SushanThakur/armikochan/3_3D_model/main-assembly.SLDASM

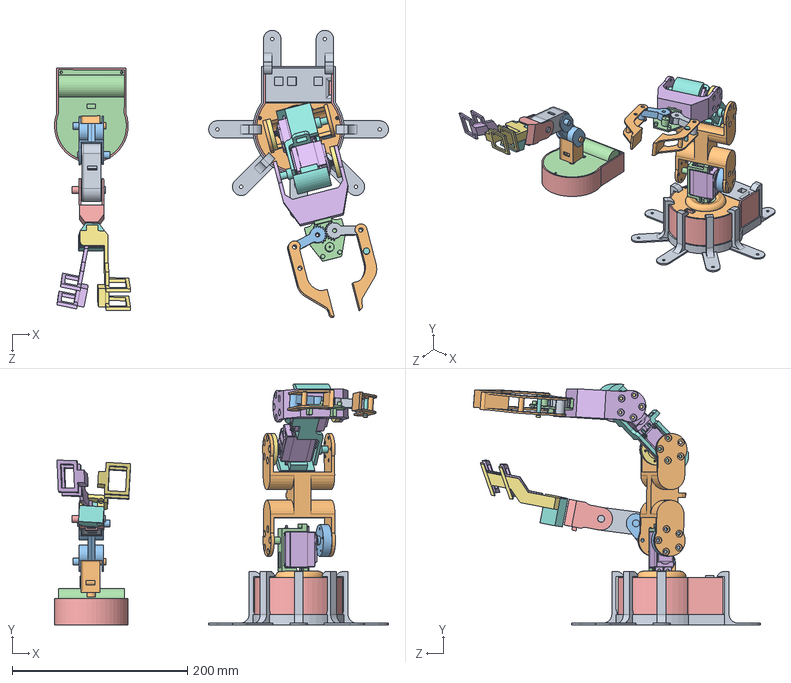
[picture p57: CAD file, 2025-09-16]
3_3D_model/main-assembly.SLDASM
380.7 x 274.4 x 327.6 mm
base
holder
left-gear-small
tip-v2 x 2
right-gear-small
holder-clip
holder-clip-holder
Servo MG996R x 4
Servo MG996R Shaft x 4
rotating_base
round-horn-extended
left-plate
base-cover
holder-arm
round-horn-self x 2
wrist-main-body
contorller-base
controller-base-cover
soldier
contorller-base-rotate
controller-arm
contorller-finger
controller-finger-tip-cover
controller-movable-finger
contorller wrist
breadboard
battery
base-cover-servo
base-supporter
