SushanThakur/armikochan/3_3D_model/controller/controller-wrist/contorller wrist.SLDPRT

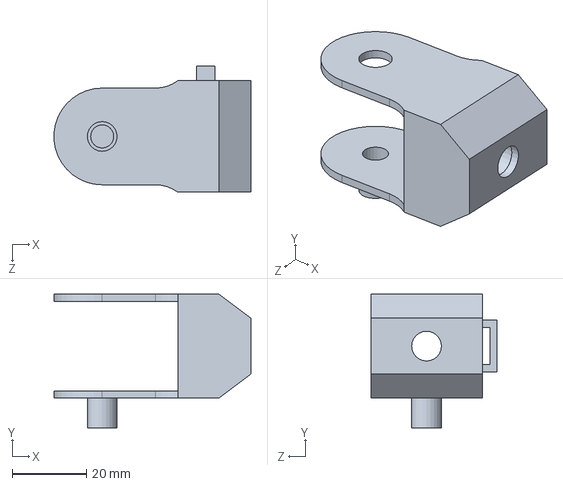
[picture p66: CAD file, 2025-09-16]
3_3D_model/controller/controller-wrist/contorller wrist.SLDPRT
53.0 x 36.0 x 34.0 mm
