SushanThakur/armikochan/3_3D_model/controller/stl/abs/controller-arm-1.STL

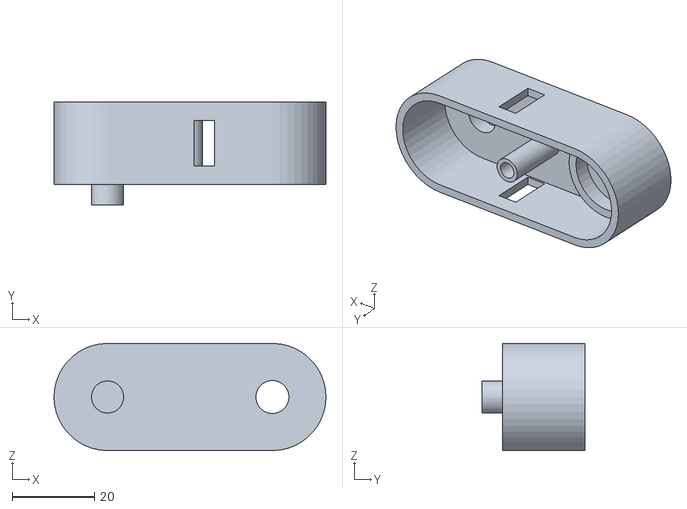
[picture p67: CAD file, 2024-01-20]
3_3D_model/controller/stl/abs/controller-arm-1.STL
66.0 x 25.0 x 26.0
