SushanThakur/armikochan/3_3D_model/shoulder/left-plate.SLDPRT

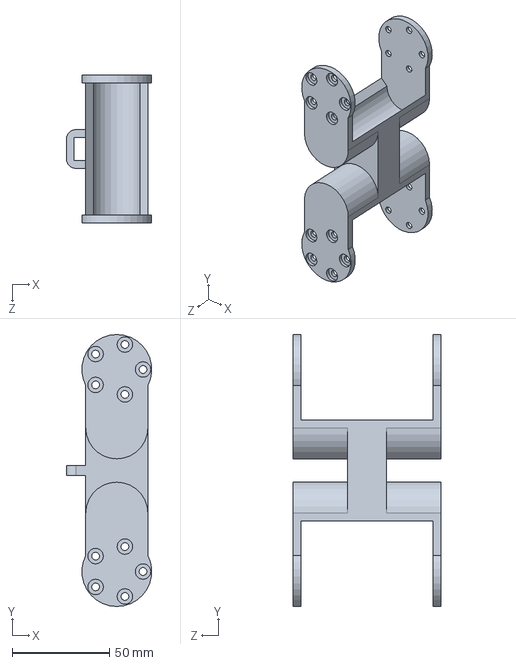
[picture p68: CAD file, 2025-09-16]
3_3D_model/shoulder/left-plate.SLDPRT
44.0 x 140.0 x 76.0 mm
