SushanThakur/armikochan/3_3D_model/test-prints/bearing-inner.SLDPRT

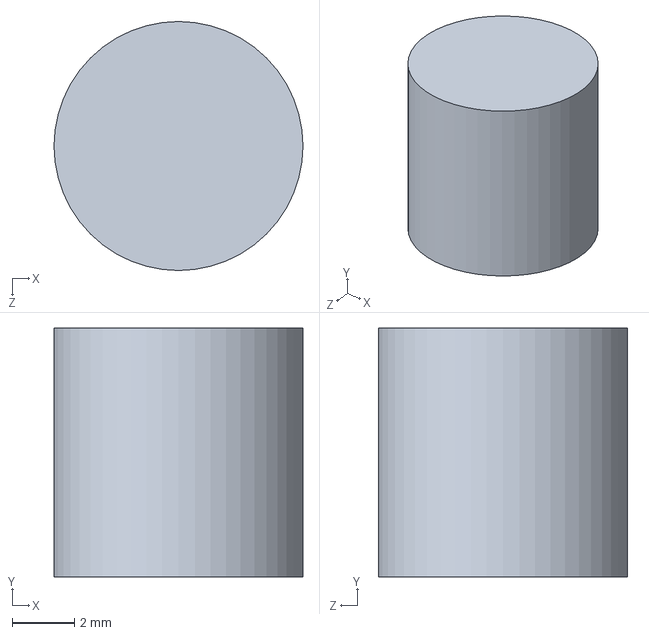
[picture p69: CAD file, 2024-01-20]
3_3D_model/test-prints/bearing-inner.SLDPRT
8.00 x 8.00 x 8.00 mm
