SushanThakur/armikochan/3_3D_model/arm/holder-arm.SLDPRT

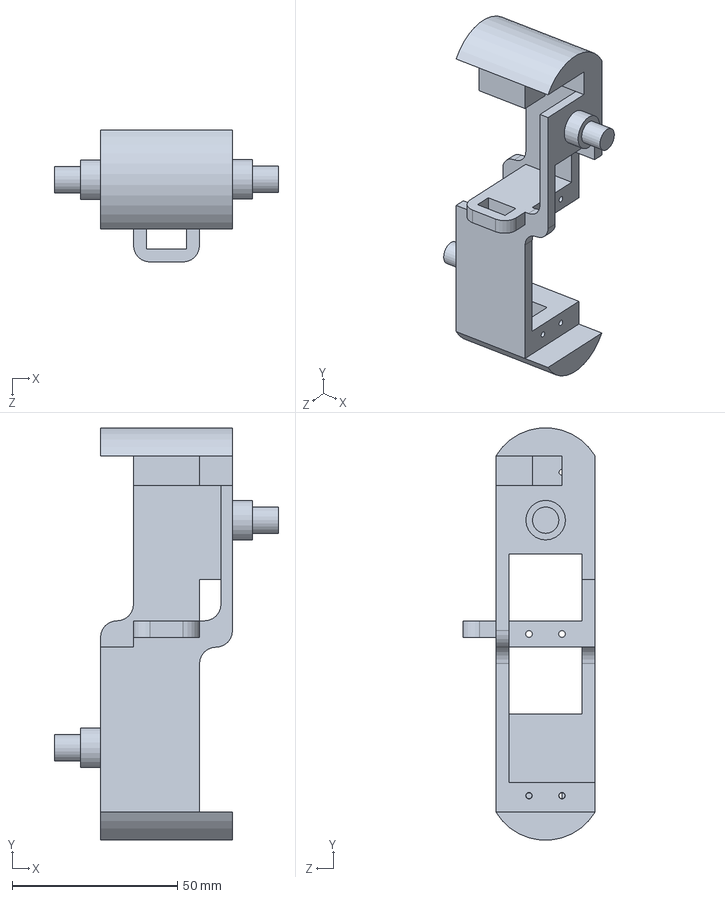
[picture p70: CAD file, 2025-09-16]
3_3D_model/arm/holder-arm.SLDPRT
68.0 x 124.8 x 40.0 mm
