SushanThakur/armikochan/3_3D_model/base-cover.SLDPRT

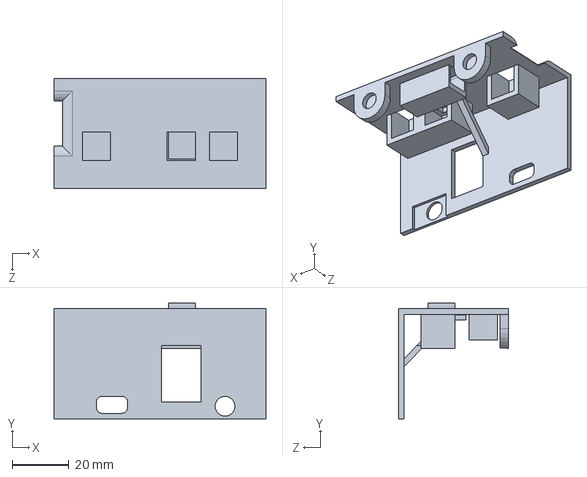
[picture p71: CAD file, 2025-09-16]
3_3D_model/base-cover.SLDPRT
75.0 x 41.0 x 39.0 mm
