SushanThakur/armikochan/3_3D_model/claw/holder-clip-holder.SLDPRT

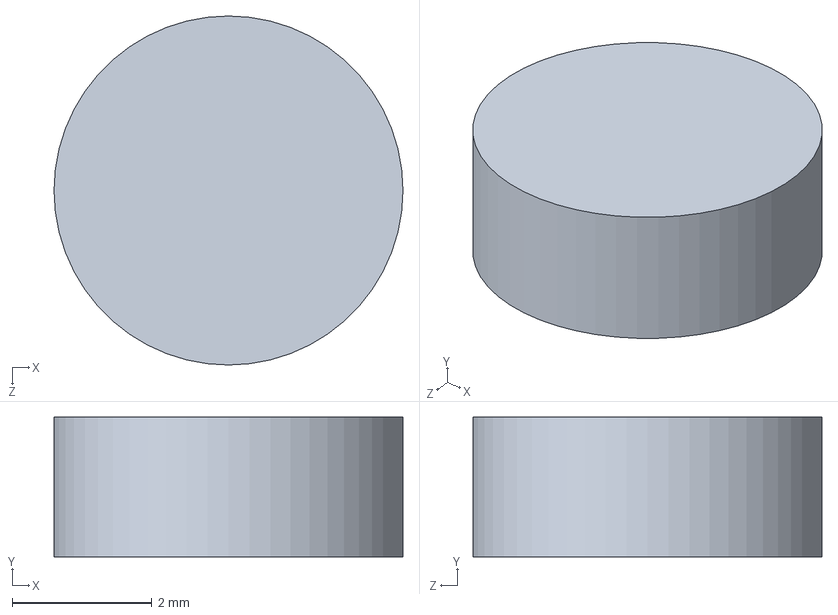
[picture p72: CAD file, 2025-09-16]
3_3D_model/claw/holder-clip-holder.SLDPRT
5.00 x 2.00 x 5.00 mm
