SushanThakur/armikochan/3_3D_model/controller/contorller-finger/controller-finger-tip-cover.SLDPRT

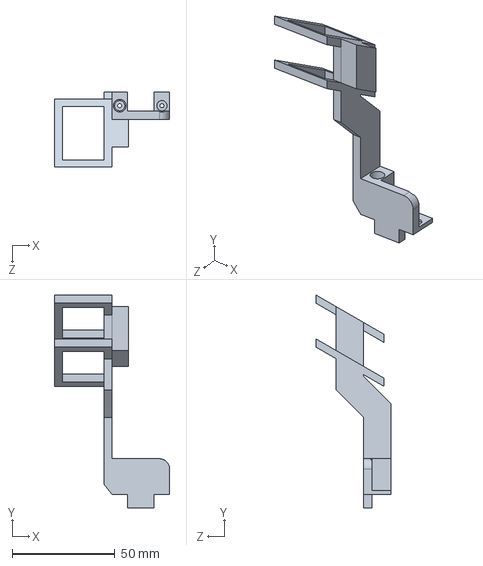
[picture p73: CAD file, 2025-09-16]
3_3D_model/controller/contorller-finger/controller-finger-tip-cover.SLDPRT
56.0 x 103.4 x 36.4 mm
