SushanThakur/armikochan/3_3D_model/controller/stl/abs/controller-arm.STL

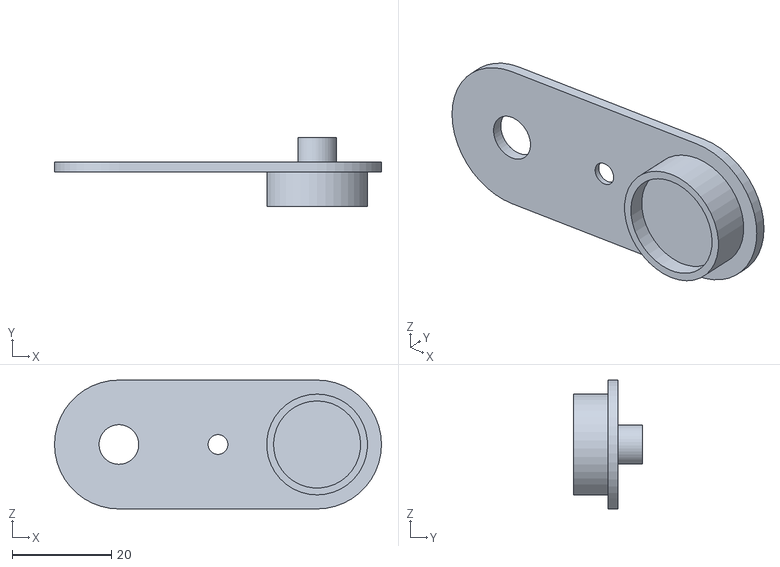
[picture p74: CAD file, 2024-01-20]
3_3D_model/controller/stl/abs/controller-arm.STL
66.0 x 14.0 x 26.0
