SushanThakur/armikochan/3_3D_model/controller/stl/second-concept-bot.STL

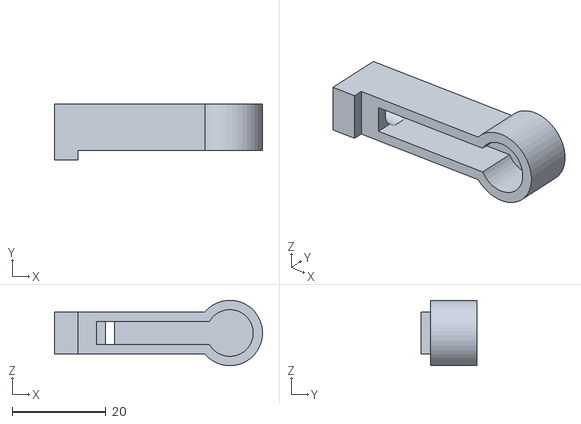
[picture p75: CAD file, 2024-02-05]
3_3D_model/controller/stl/second-concept-bot.STL
44.5 x 12.0 x 14.0
