SushanThakur/armikochan/3_3D_model/MG996R SERVO/Servo MG996R.SLDPRT

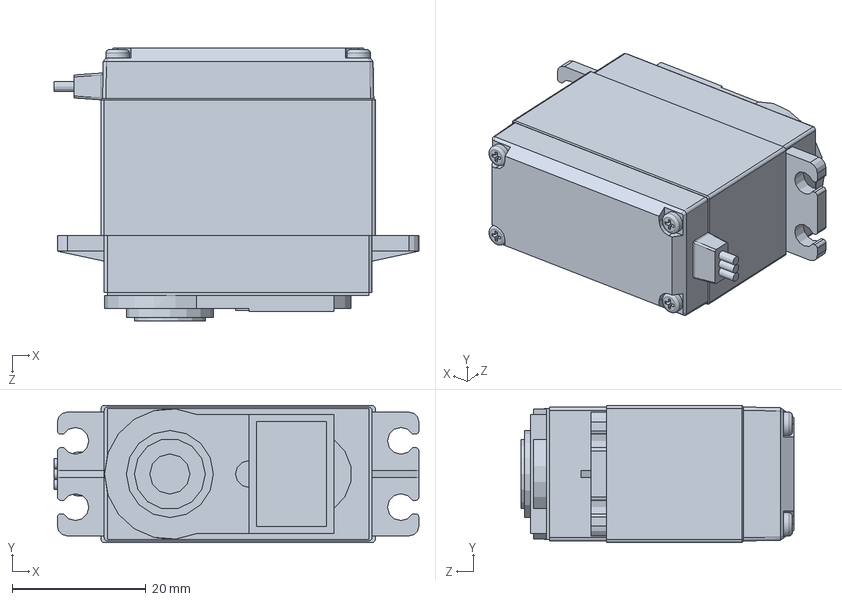
[picture p76: CAD file, 2025-09-16]
3_3D_model/MG996R SERVO/Servo MG996R.SLDPRT
54.5 x 20.5 x 40.7 mm
