SushanThakur/armikochan/3_3D_model/stl/round-horn-self-v2.STL

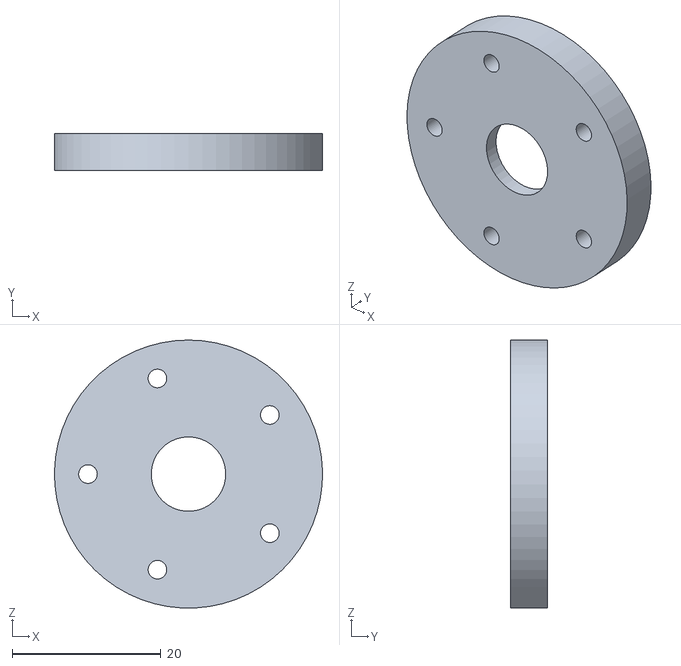
[picture p77: CAD file, 2024-01-21]
3_3D_model/stl/round-horn-self-v2.STL
36.0 x 5.00 x 36.0
