SushanThakur/armikochan/3_3D_model/test-prints/test-print.3mf

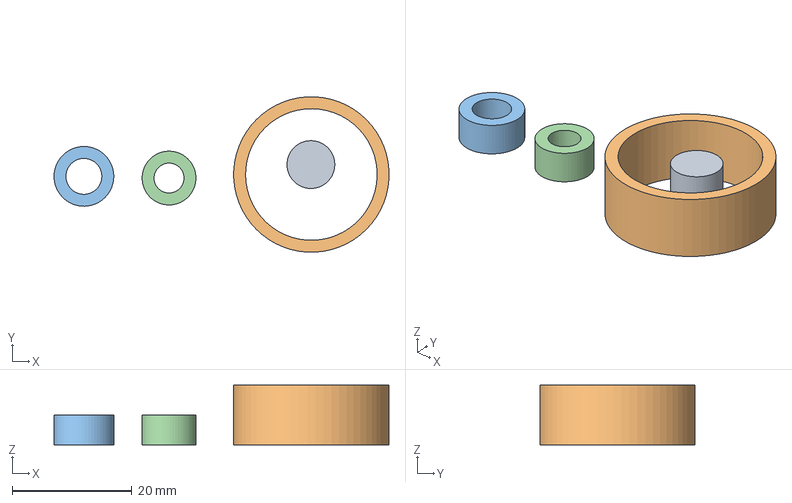
[picture p78: CAD file, 2024-01-20]
3_3D_model/test-prints/test-print.3mf
56.0 x 26.0 x 10.0 mm
bearing-inner.STL
bearing-outer.STL
mg996r.STL
micro-servo.STL
