SushanThakur/armikochan/3_3D_model/claw/right-gear-small.SLDPRT

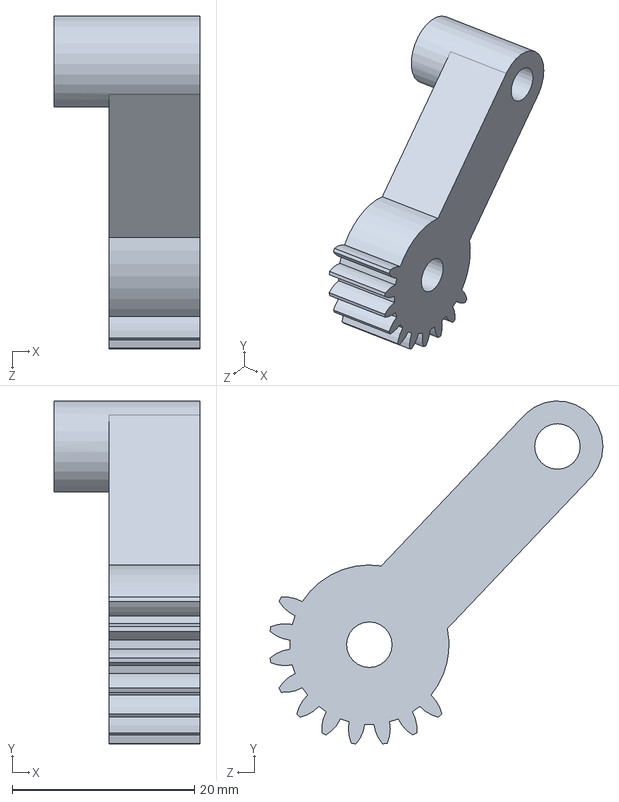
[picture p79: CAD file, 2025-09-16]
3_3D_model/claw/right-gear-small.SLDPRT
16.0 x 37.7 x 36.6 mm
