SushanThakur/armikochan/3_3D_model/controller/battery.SLDPRT

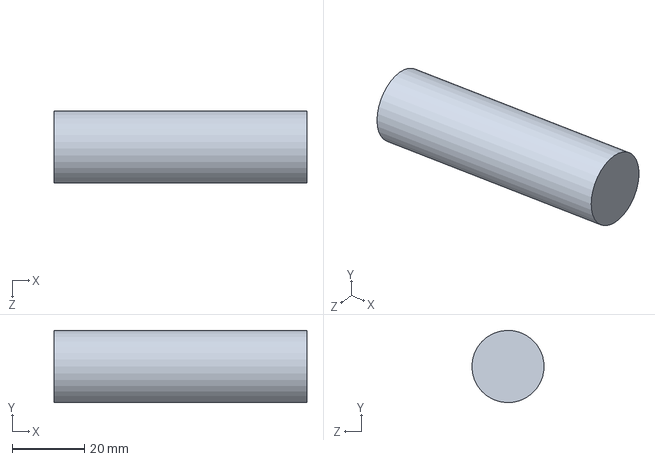
[picture p80: CAD file, 2025-09-16]
3_3D_model/controller/battery.SLDPRT
70.0 x 20.0 x 20.0 mm
