SushanThakur/armikochan/3_3D_model/controller/contorller-finger/controller-movable-finger.SLDPRT

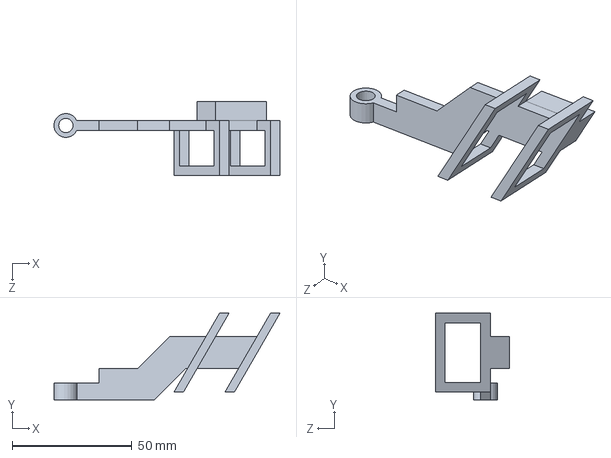
[picture p81: CAD file, 2025-09-16]
3_3D_model/controller/contorller-finger/controller-movable-finger.SLDPRT
94.5 x 36.2 x 31.1 mm
