SushanThakur/armikochan/3_3D_model/controller/stl/abs/contorller-base-rotate.STL

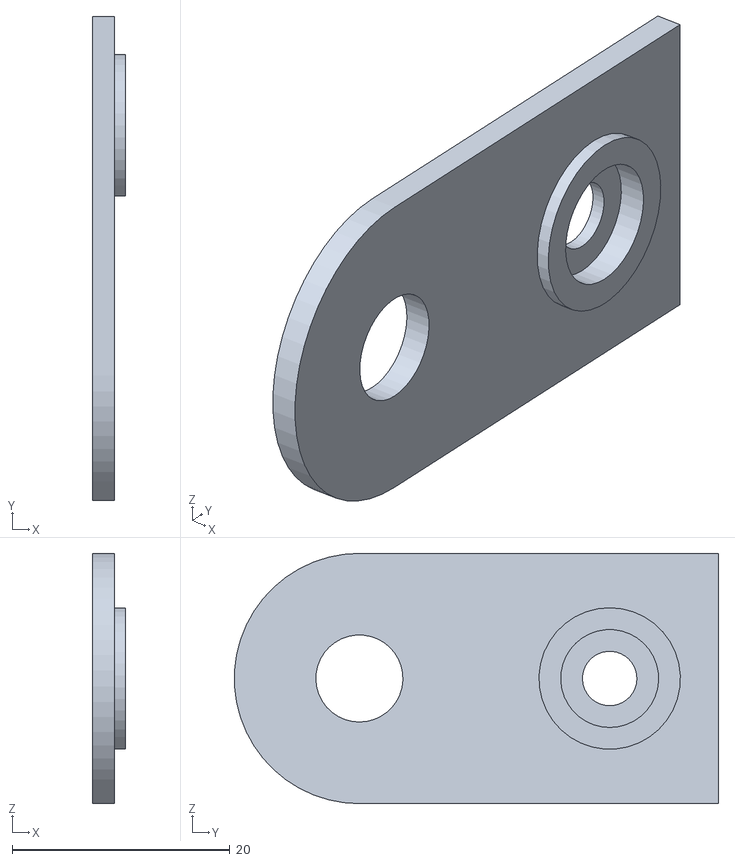
[picture p82: CAD file, 2024-01-20]
3_3D_model/controller/stl/abs/contorller-base-rotate.STL
3.00 x 44.5 x 23.0
