SushanThakur/armikochan/3_3D_model/controller/stl/second-concept-top.STL

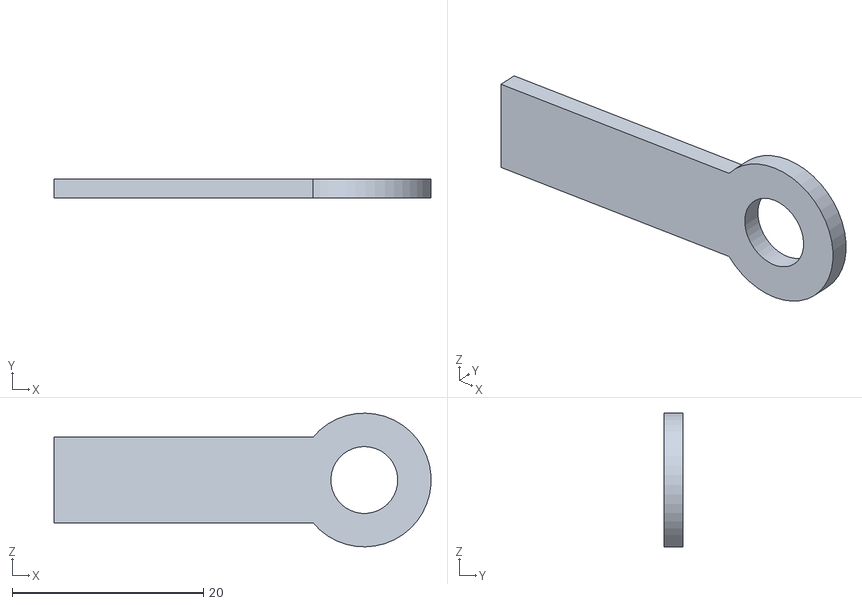
[picture p83: CAD file, 2024-02-05]
3_3D_model/controller/stl/second-concept-top.STL
39.5 x 2.00 x 14.0
