SushanThakur/armikochan/3_3D_model/MG996R SERVO/Servo MG996R Shaft.SLDPRT

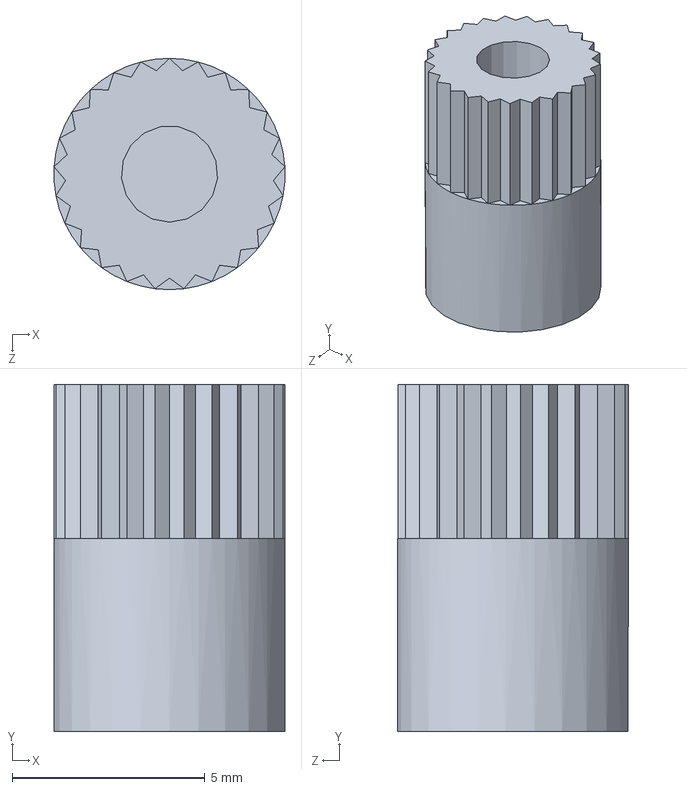
[picture p84: CAD file, 2025-09-16]
3_3D_model/MG996R SERVO/Servo MG996R Shaft.SLDPRT
5.99 x 9.00 x 6.00 mm
