SushanThakur/armikochan/3_3D_model/test-prints/micro-servo.SLDPRT

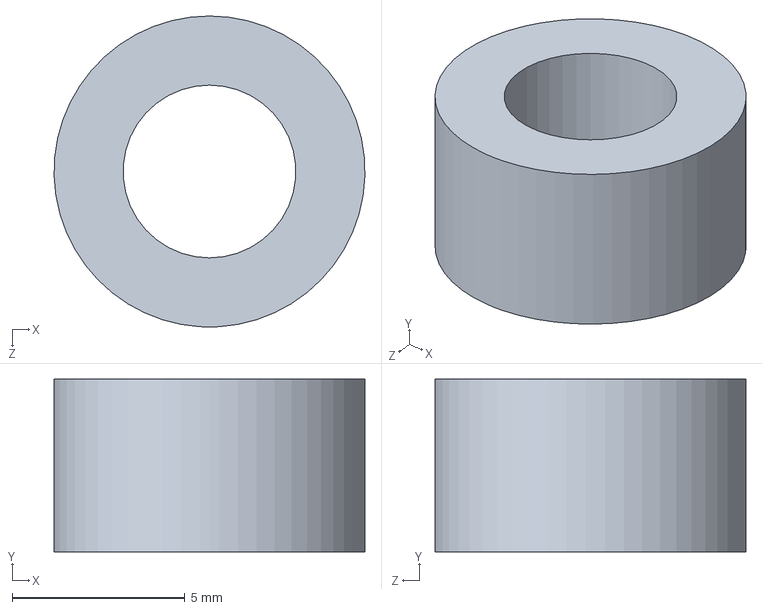
[picture p85: CAD file, 2024-01-20]
3_3D_model/test-prints/micro-servo.SLDPRT
9.00 x 5.00 x 9.00 mm
