SushanThakur/armikochan/3_3D_model/base-supporter.SLDPRT

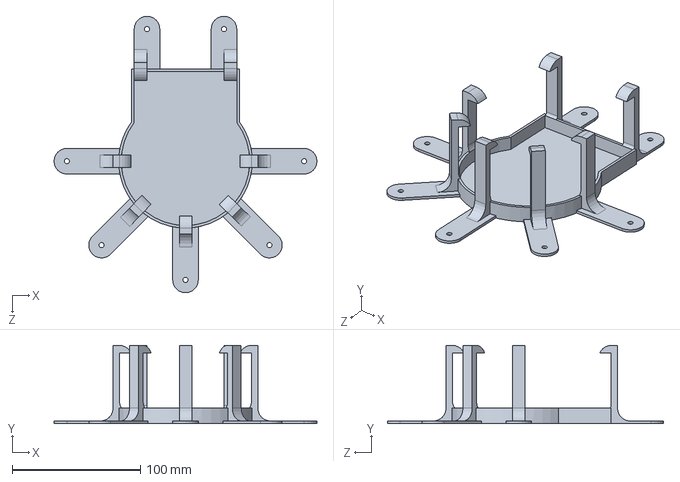
[picture p86: CAD file, 2025-09-16]
3_3D_model/base-supporter.SLDPRT
205.0 x 61.0 x 215.5 mm
