SushanThakur/armikochan/3_3D_model/claw/mg90s.SLDPRT

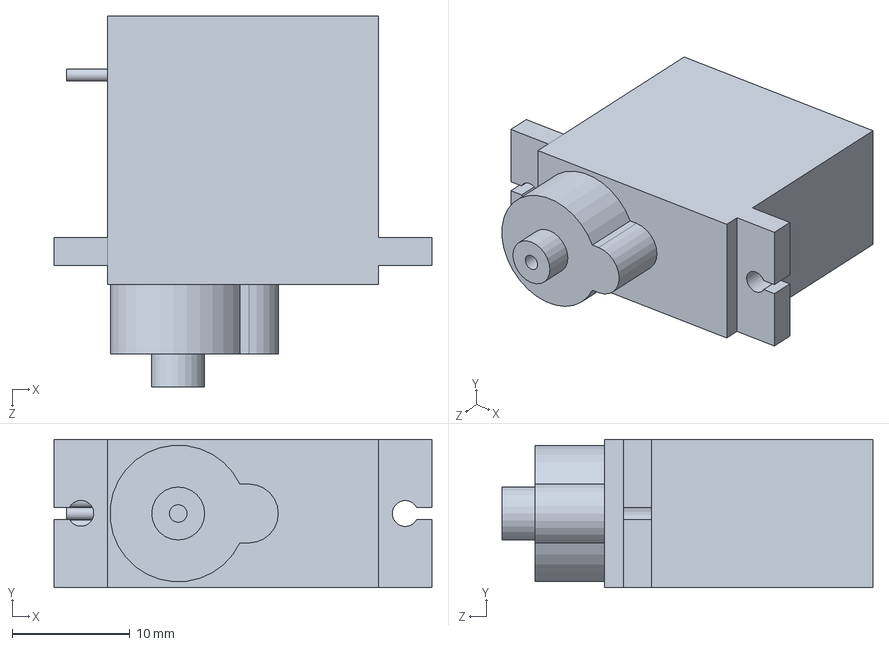
[picture p87: CAD file, 2025-09-16]
3_3D_model/claw/mg90s.SLDPRT
32.1 x 12.6 x 31.5 mm
