SushanThakur/armikochan/3_3D_model/controller/breadboard.SLDPRT

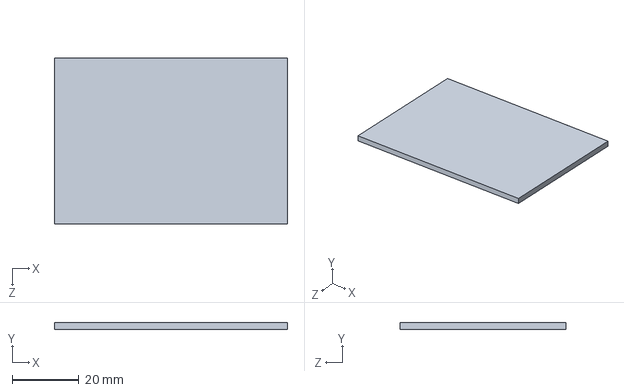
[picture p88: CAD file, 2025-09-16]
3_3D_model/controller/breadboard.SLDPRT
70.0 x 2.00 x 50.0 mm
