SushanThakur/armikochan/3_3D_model/controller/contorller-finger/controller-movable-finger-tip-holder.SLDPRT

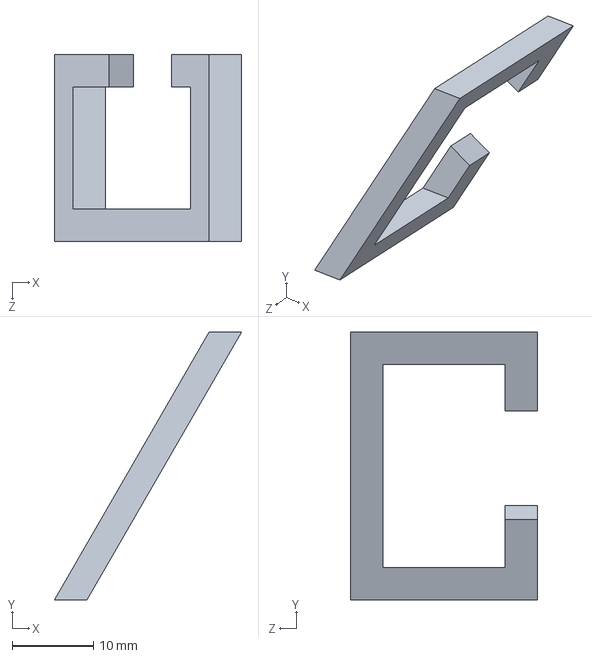
[picture p89: CAD file, 2024-02-05]
3_3D_model/controller/contorller-finger/controller-movable-finger-tip-holder.SLDPRT
23.0 x 32.9 x 23.0 mm
