SushanThakur/armikochan/3_3D_model/controller/stl/abs/contorller-base-rotate-1.STL

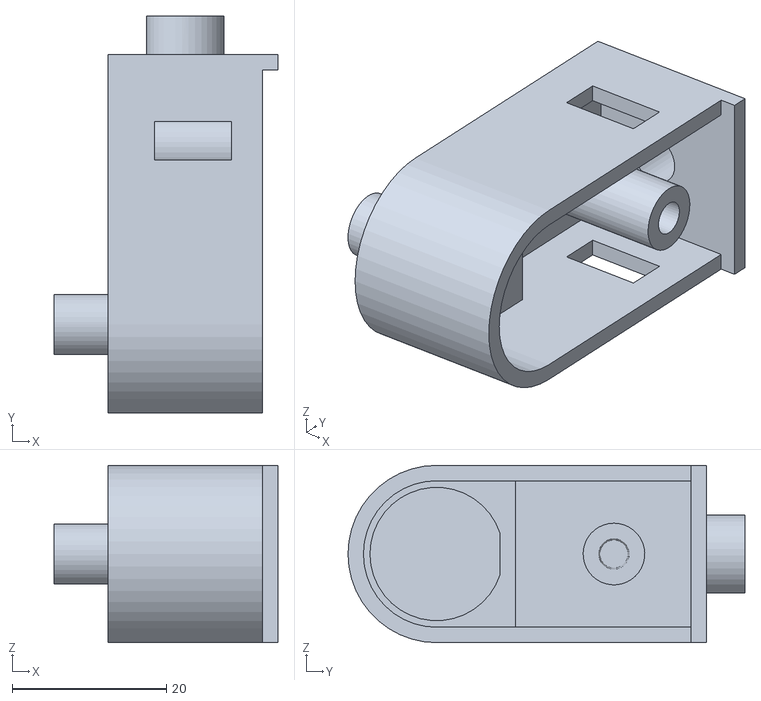
[picture p90: CAD file, 2024-01-20]
3_3D_model/controller/stl/abs/contorller-base-rotate-1.STL
29.0 x 51.5 x 23.0
