SushanThakur/armikochan/3_3D_model/MG996R SERVO/Servo MG996R arm01.SLDPRT

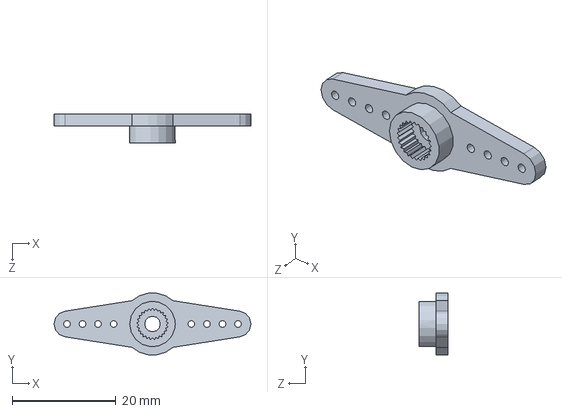
[picture p91: CAD file, 2023-12-06]
3_3D_model/MG996R SERVO/Servo MG996R arm01.SLDPRT
38.0 x 11.9 x 5.50 mm
