SushanThakur/armikochan/3_3D_model/test-prints/bearing-outer.SLDPRT

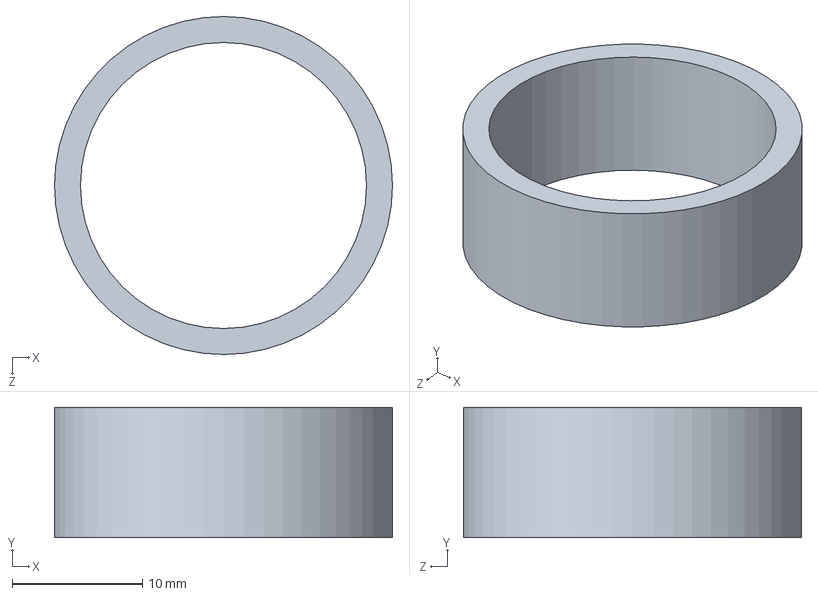
[picture p92: CAD file, 2024-01-20]
3_3D_model/test-prints/bearing-outer.SLDPRT
26.0 x 10.0 x 26.0 mm
