SushanThakur/armikochan/3_3D_model/base-joint/round-horn-extended.SLDPRT

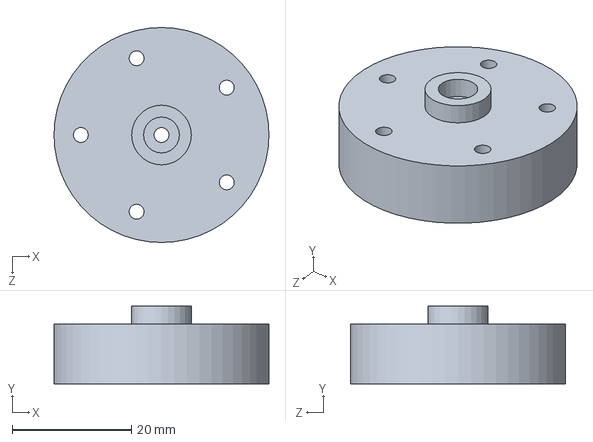
[picture p93: CAD file, 2025-09-16]
3_3D_model/base-joint/round-horn-extended.SLDPRT
36.0 x 13.0 x 36.0 mm
