SushanThakur/armikochan/3_3D_model/base.SLDPRT

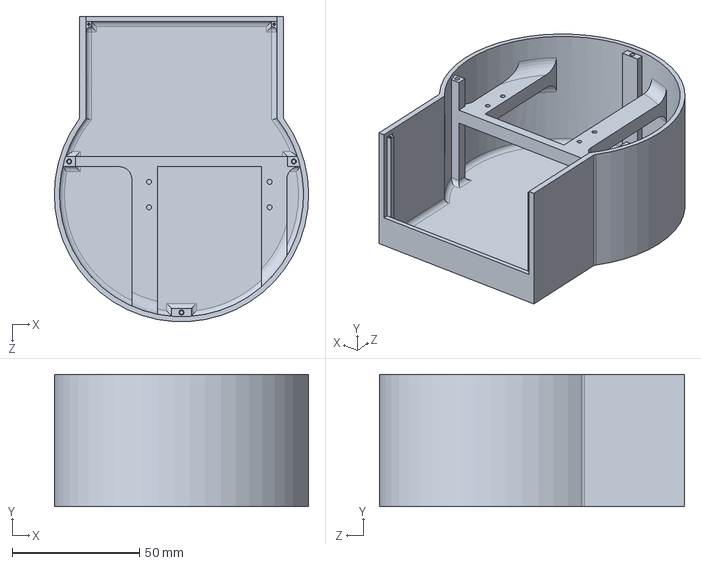
[picture p94: CAD file, 2025-09-16]
3_3D_model/base.SLDPRT
100.0 x 52.0 x 119.9 mm
