SushanThakur/armikochan/3_3D_model/claw/left-gear-small.SLDPRT

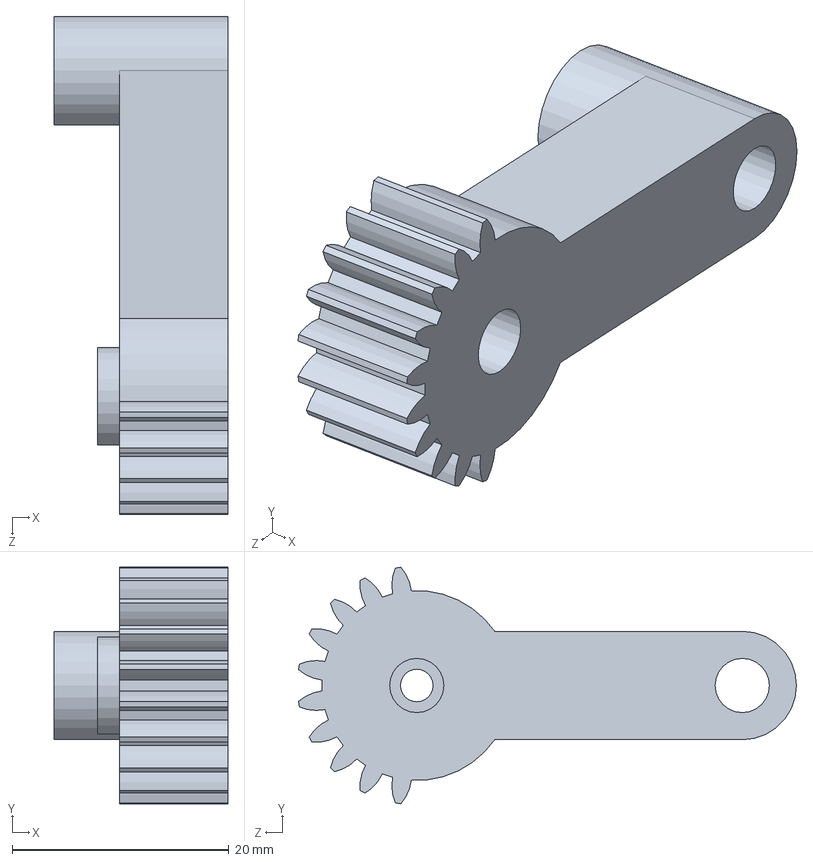
[picture p95: CAD file, 2025-09-16]
3_3D_model/claw/left-gear-small.SLDPRT
16.0 x 21.8 x 45.9 mm
