SushanThakur/armikochan/3_3D_model/controller/contorller-finger/second-concept.SLDPRT

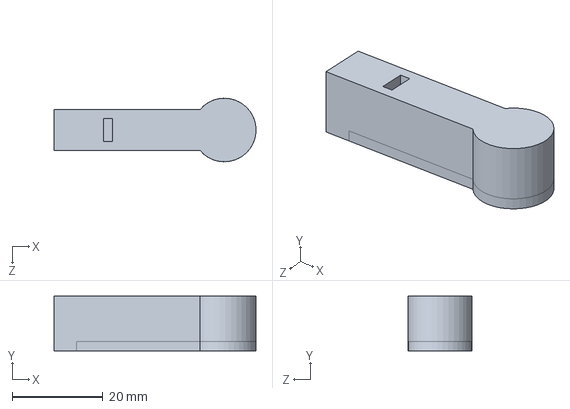
[picture p96: CAD file, 2024-02-05]
3_3D_model/controller/contorller-finger/second-concept.SLDPRT
44.5 x 12.0 x 14.0 mm
