SushanThakur/armikochan/3_3D_model/controller/controller-base-cover.SLDPRT

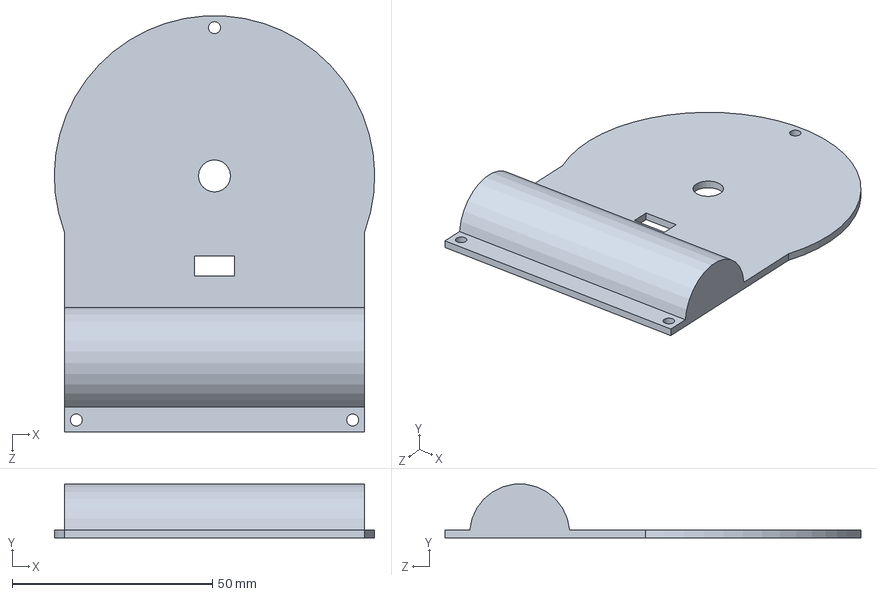
[picture p97: CAD file, 2025-09-16]
3_3D_model/controller/controller-base-cover.SLDPRT
80.0 x 13.4 x 103.8 mm
