SushanThakur/armikochan/3_3D_model/test-prints/mg996r.SLDPRT

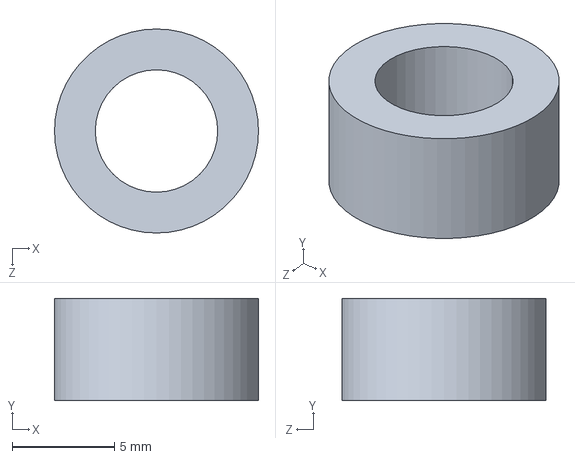
[picture p98: CAD file, 2024-01-20]
3_3D_model/test-prints/mg996r.SLDPRT
10.0 x 5.00 x 10.0 mm
