SushanThakur/armikochan/3_3D_model/base-cover-bttn-v2.SLDPRT

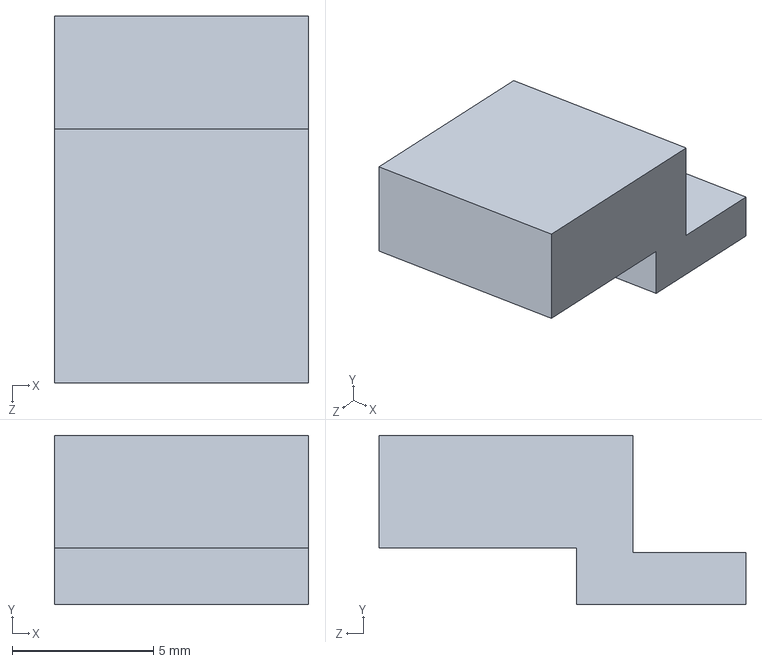
[picture p99: CAD file, 2024-01-20]
3_3D_model/base-cover-bttn-v2.SLDPRT
9.00 x 6.00 x 13.0 mm
