SushanThakur/armikochan/3_3D_model/claw/holder-clip.SLDPRT

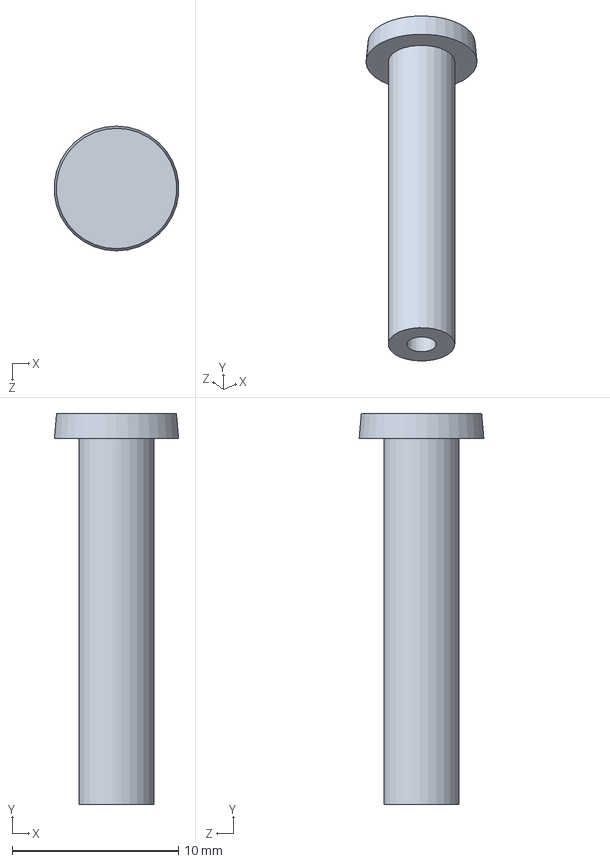
[picture p100: CAD file, 2025-09-16]
3_3D_model/claw/holder-clip.SLDPRT
7.47 x 23.5 x 7.50 mm
