SushanThakur/armikochan/3_3D_model/controller/soldier.SLDPRT

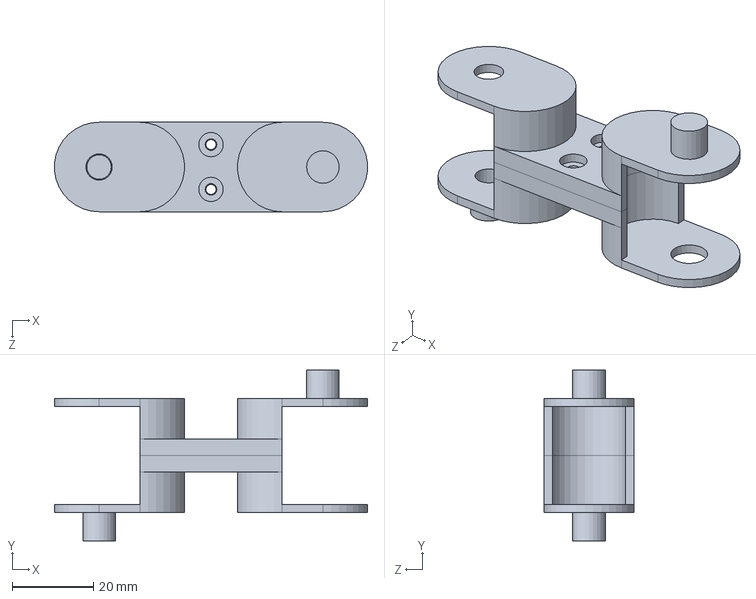
[picture p101: CAD file, 2025-09-16]
3_3D_model/controller/soldier.SLDPRT
76.9 x 42.0 x 22.0 mm
