SushanThakur/armikochan/3_3D_model/base-joint/rotating-base-cover.SLDPRT

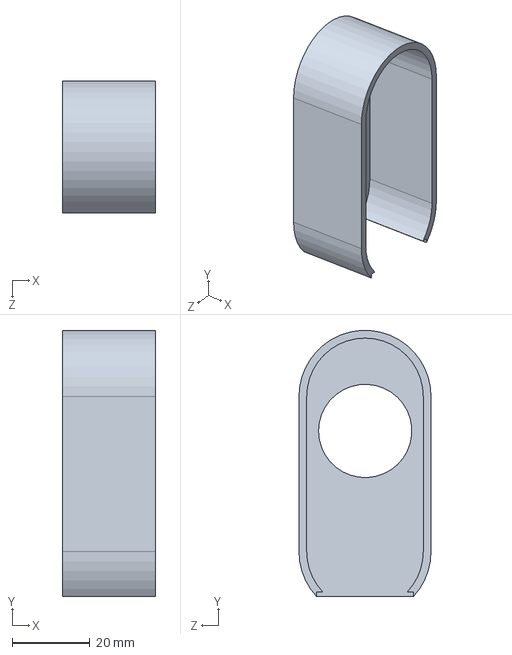
[picture p102: CAD file, 2024-01-20]
3_3D_model/base-joint/rotating-base-cover.SLDPRT
24.0 x 68.5 x 34.0 mm
