SushanThakur/armikochan/3_3D_model/claw/holder.SLDPRT

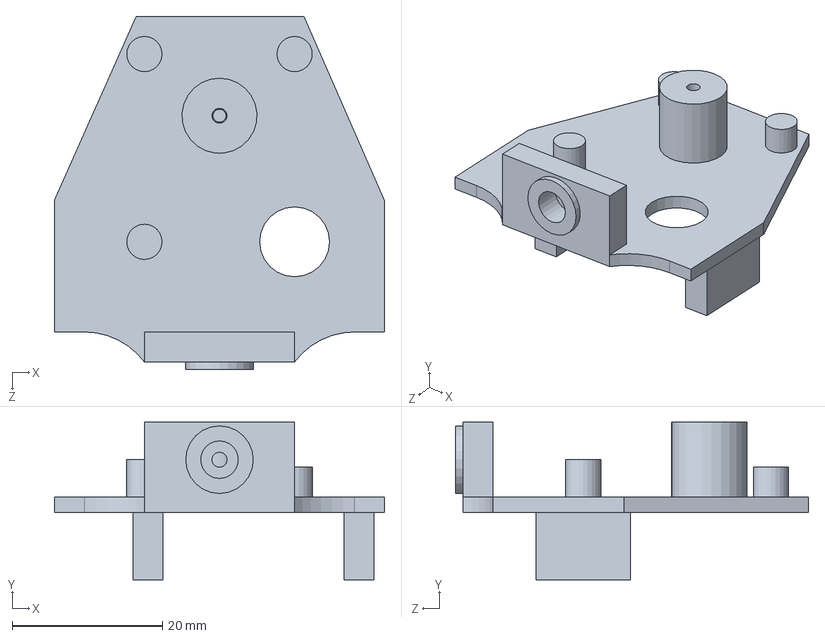
[picture p103: CAD file, 2025-09-16]
3_3D_model/claw/holder.SLDPRT
44.0 x 21.0 x 47.0 mm
