SushanThakur/armikochan/3_3D_model/controller/POT10K.step

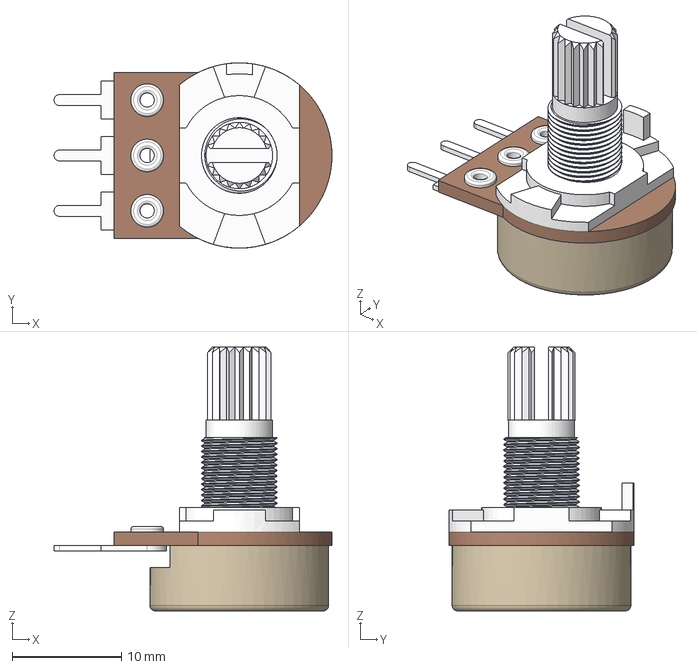
[picture p104: CAD file, 2024-01-20]
3_3D_model/controller/POT10K.step
25.5 x 17.0 x 24.2 mm
