SushanThakur/armikochan/3_3D_model/controller/stl/soldier-top.STL

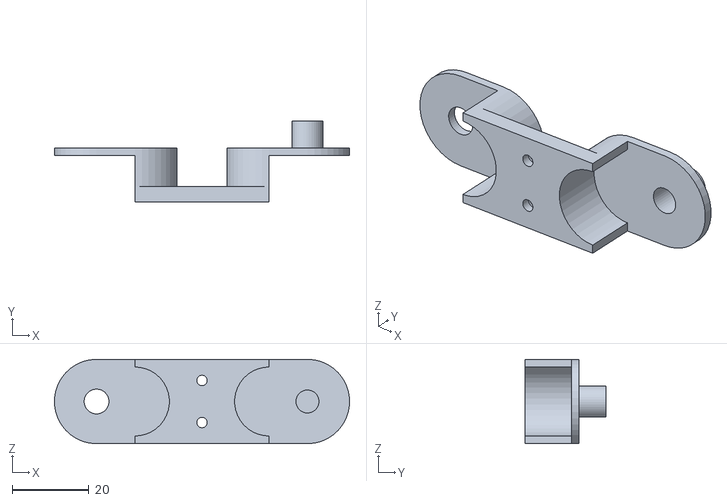
[picture p105: CAD file, 2024-01-20]
3_3D_model/controller/stl/soldier-top.STL
76.9 x 21.0 x 22.0
