SushanThakur/armikochan/3_3D_model/claw/tip-v2.SLDPRT

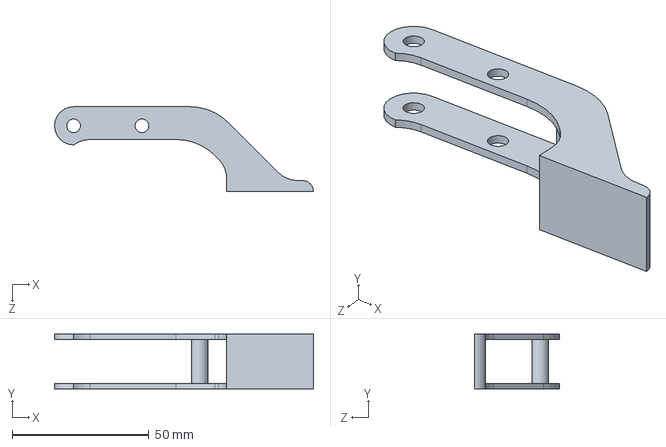
[picture p106: CAD file, 2025-09-16]
3_3D_model/claw/tip-v2.SLDPRT
94.8 x 20.0 x 31.0 mm
