SushanThakur/armikochan/3_3D_model/claw/left-holder.SLDPRT

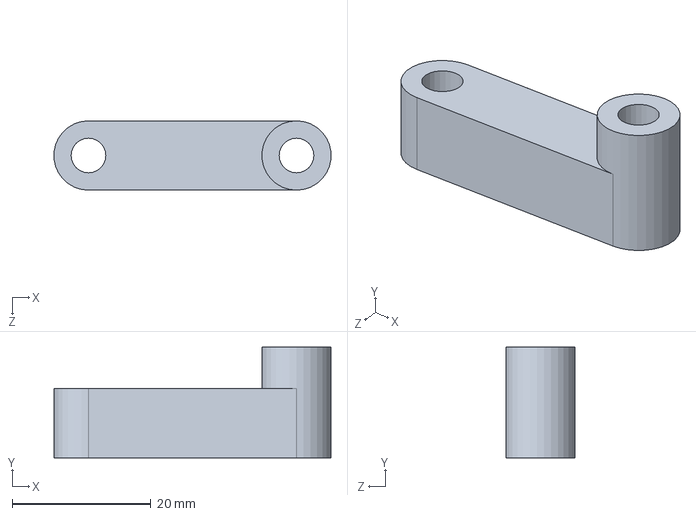
[picture p107: CAD file, 2025-09-16]
3_3D_model/claw/left-holder.SLDPRT
39.9 x 16.0 x 10.0 mm
