SushanThakur/armikochan/3_3D_model/claw/cover.SLDPRT

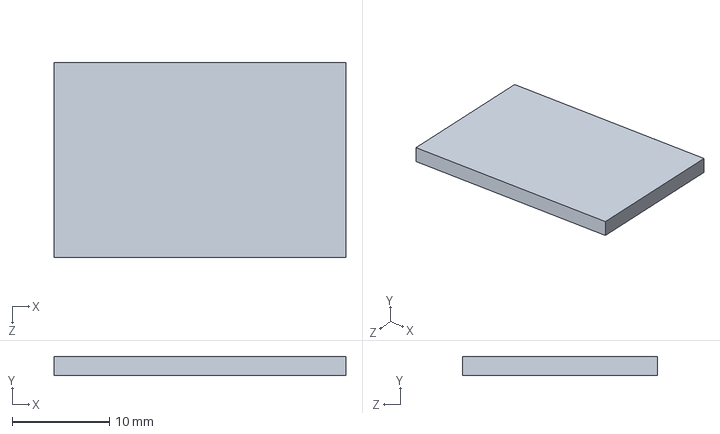
[picture p108: CAD file, 2024-01-20]
3_3D_model/claw/cover.SLDPRT
30.0 x 2.00 x 20.0 mm
