SushanThakur/armikochan/3_3D_model/claw/right-gear.SLDPRT

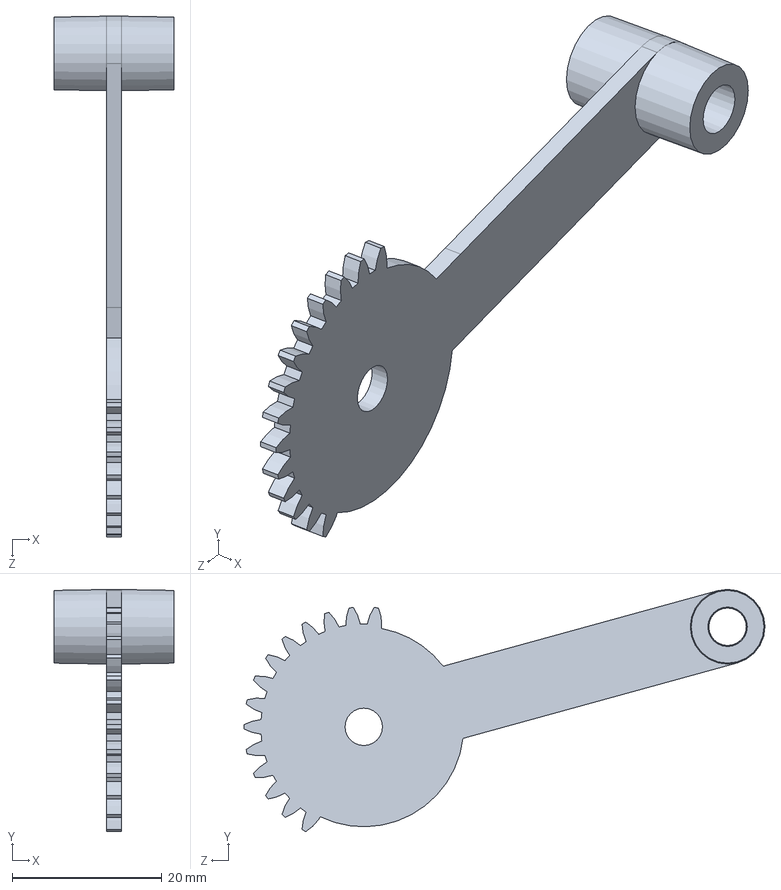
[picture p109: CAD file, 2023-12-06]
3_3D_model/claw/right-gear.SLDPRT
16.0 x 32.4 x 69.6 mm
