SushanThakur/armikochan/3_3D_model/stl/base-cover-led-cover.STL

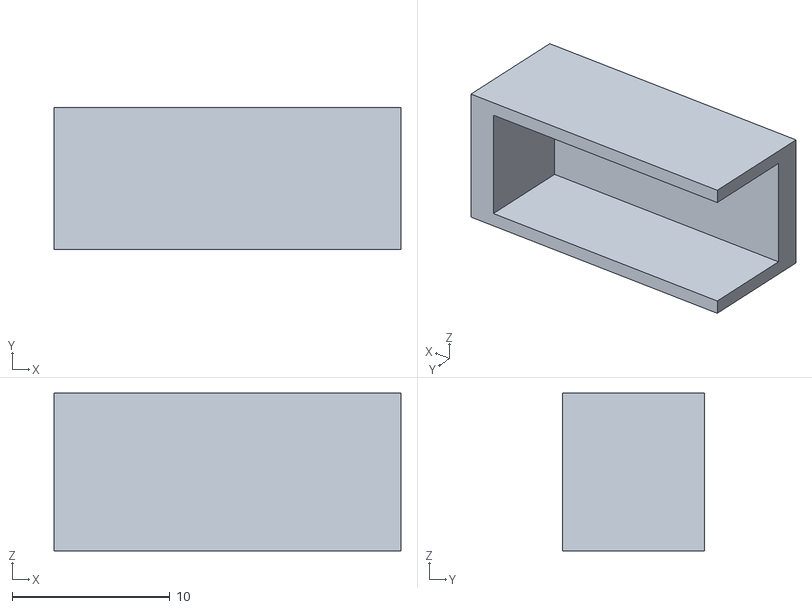
[picture p110: CAD file, 2024-01-20]
3_3D_model/stl/base-cover-led-cover.STL
22.0 x 9.00 x 10.00
