SushanThakur/armikochan/3_3D_model/claw/gear-module-1.SLDPRT

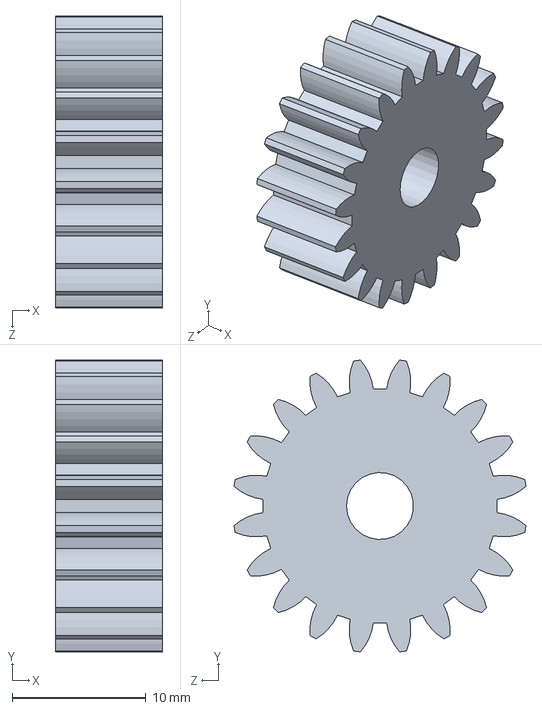
[picture p111: CAD file, 2023-12-06]
3_3D_model/claw/gear-module-1.SLDPRT
8.00 x 21.8 x 21.8 mm
