SushanThakur/armikochan/3_3D_model/claw/left-gear.SLDPRT

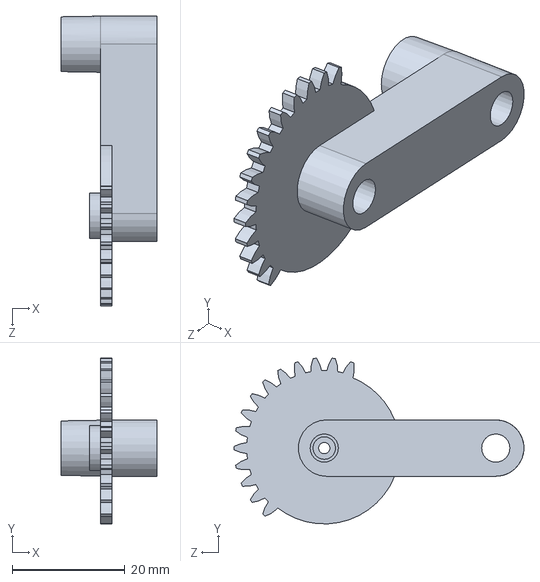
[picture p112: CAD file, 2023-12-06]
3_3D_model/claw/left-gear.SLDPRT
17.0 x 29.4 x 51.4 mm
