SushanThakur/armikochan/3_3D_model/stl/holder-clip.STL

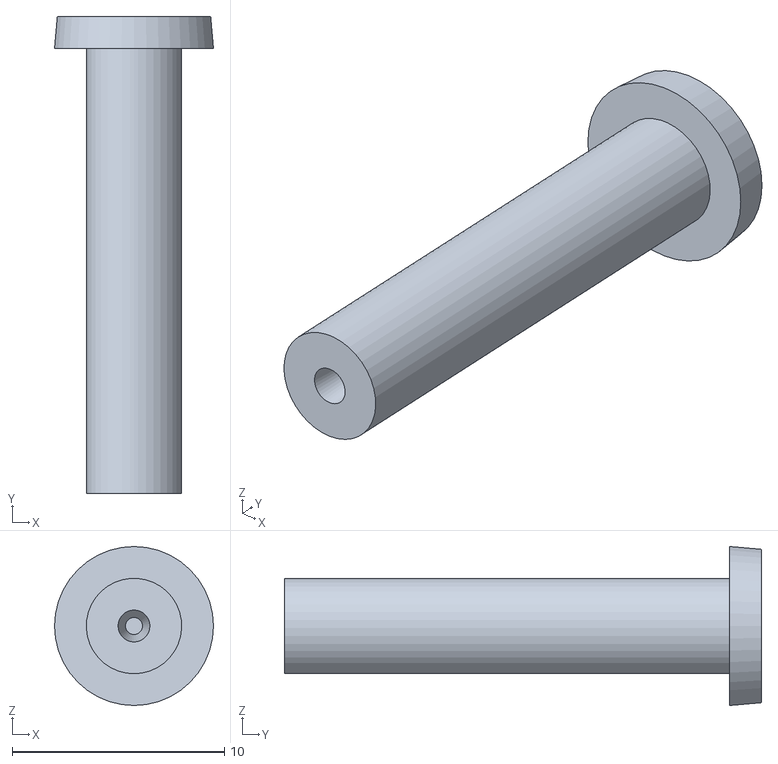
[picture p113: CAD file, 2023-12-06]
3_3D_model/stl/holder-clip.STL
7.50 x 22.5 x 7.50
