SushanThakur/armikochan/3_3D_model/claw/right-holder.SLDPRT

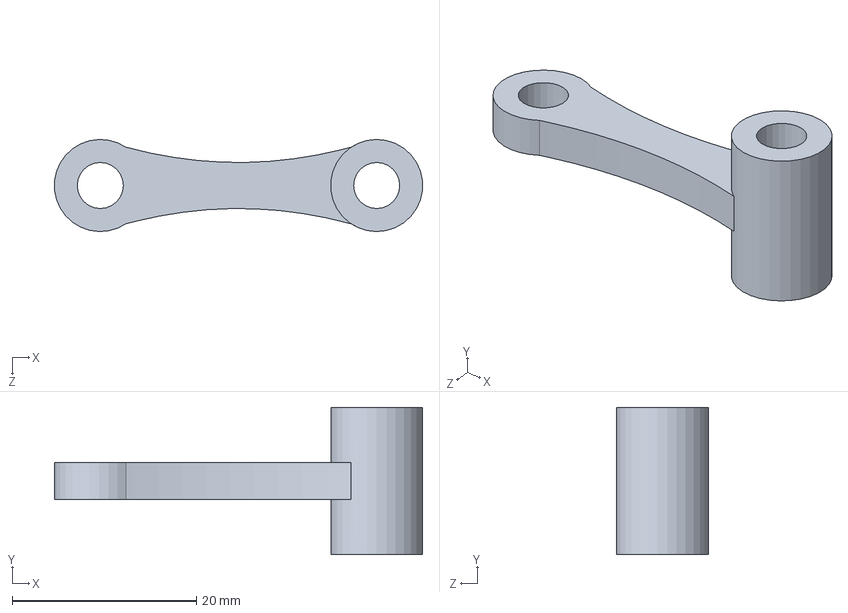
[picture p114: CAD file, 2023-12-06]
3_3D_model/claw/right-holder.SLDPRT
39.9 x 16.0 x 10.0 mm
