SushanThakur/armikochan/3_3D_model/claw/finger-tip.SLDPRT

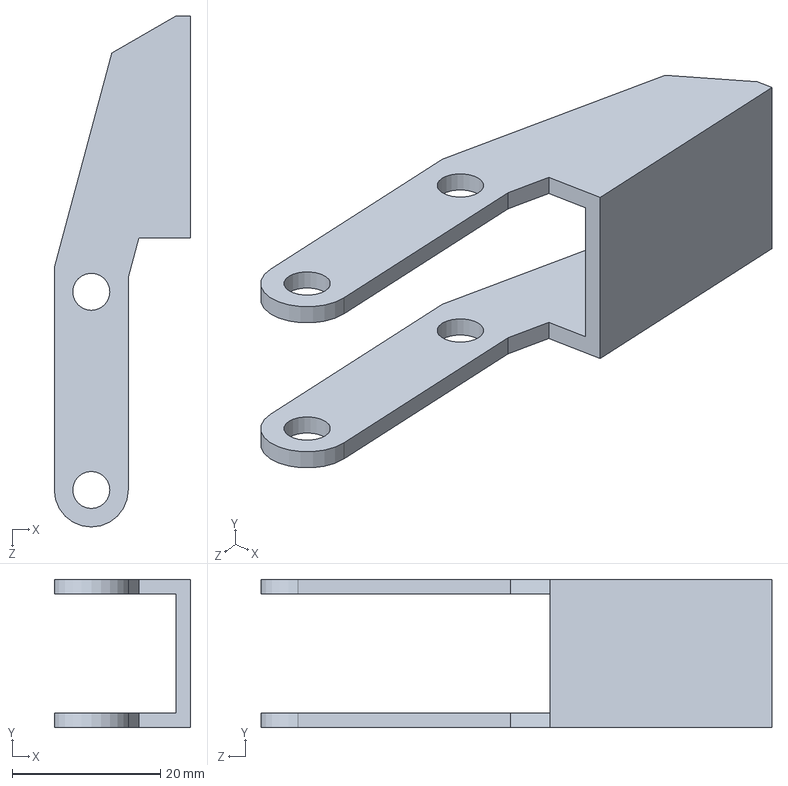
[picture p115: CAD file, 2023-12-04]
3_3D_model/claw/finger-tip.SLDPRT
18.4 x 20.0 x 69.0 mm
