SushanThakur/armikochan/4_test_codes/led-test/led-test.ino

int redPin = 4;
int greenPin = 2;
int bluePin = 15;

void setup() {
  pinMode(redPin, OUTPUT);
  pinMode(greenPin, OUTPUT);
  pinMode(bluePin, OUTPUT);

}

void loop() {
  setColor(255, 0, 0);
  delay(500);
  setColor(0, 255, 0);
  delay(500);
  setColor(0,0,255);
  delay(500);
  setColor(255,255,255);
  delay(500);
  setColor(170,0,255);
  delay(500);
}

void setColor(int r, int g, int b) {
  analogWrite(redPin, r);
  analogWrite(greenPin, g);
  analogWrite(bluePin, b);
}
